amperka/abot/cad/MOTORS/12.SLDPRT

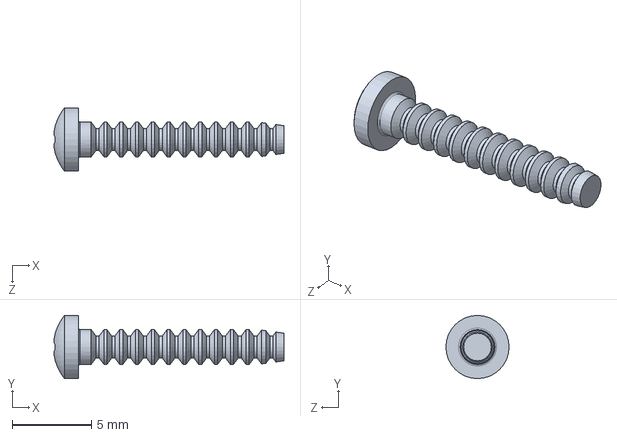
[picture p10: CAD file, 2021-09-09]
cad/MOTORS/12.SLDPRT
14.6 x 4.00 x 4.00 mm
