amperka/abot/cad/PARTS_PRINT/COMMON_PARTS/PRINT_PLATE_0.SLDPRT

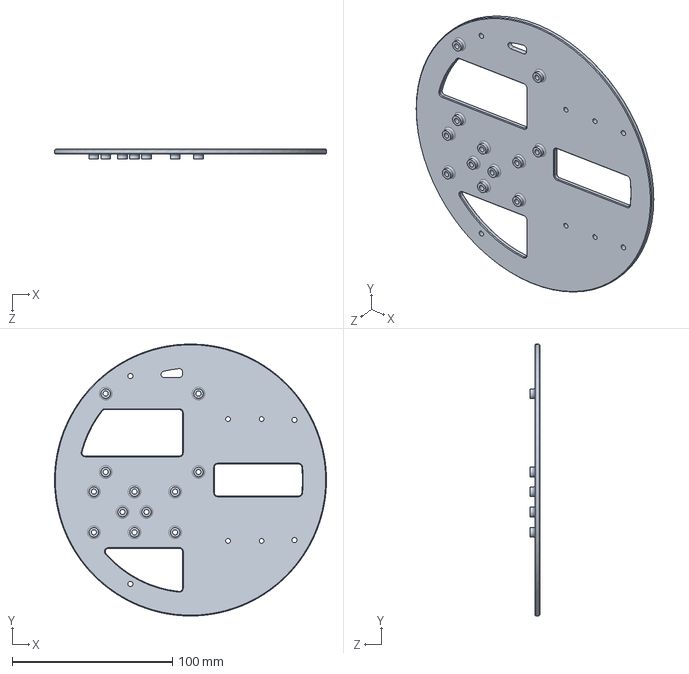
[picture p11: CAD file, 2021-09-09]
cad/PARTS_PRINT/COMMON_PARTS/PRINT_PLATE_0.SLDPRT
170.0 x 170.0 x 6.00 mm
