amperka/abot/cad/PARTS_PRINT/SHARP_IR_HOLDER.SLDPRT

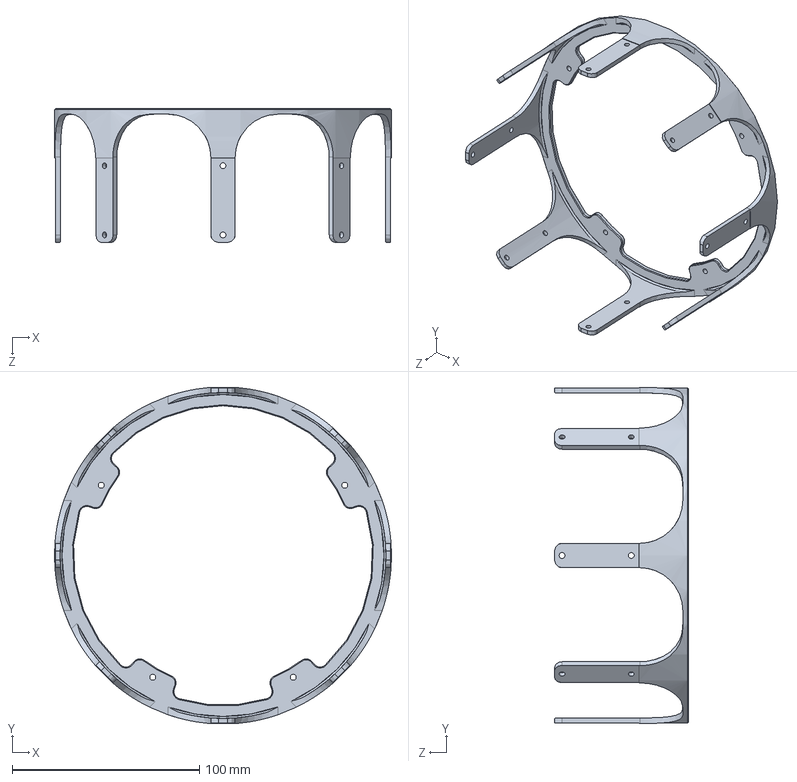
[picture p12: CAD file, 2021-09-09]
cad/PARTS_PRINT/SHARP_IR_HOLDER.SLDPRT
180.0 x 179.5 x 71.5 mm
