amperka/abot/cad/PARTS_PRINT/SOUND_PARTS/PRINT_MIC_CAP.SLDPRT

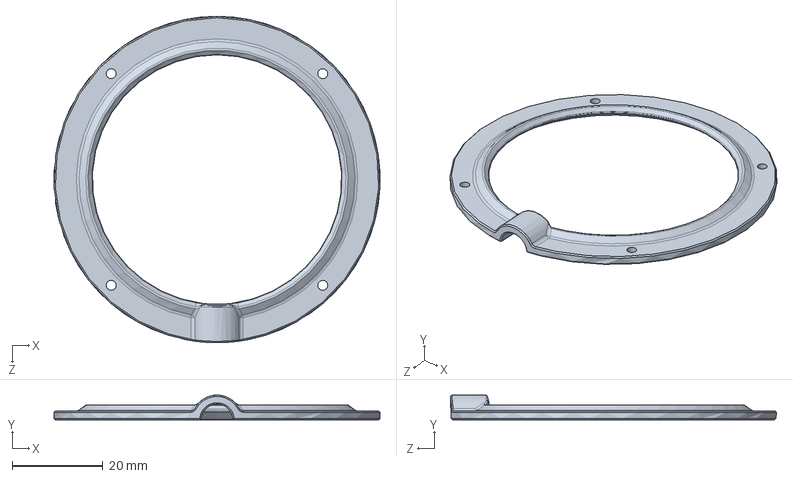
[picture p13: CAD file, 2021-09-09]
cad/PARTS_PRINT/SOUND_PARTS/PRINT_MIC_CAP.SLDPRT
71.9 x 5.50 x 72.0 mm
