amperka/abot/cad/SENSORS/LIDAR/18.SLDPRT

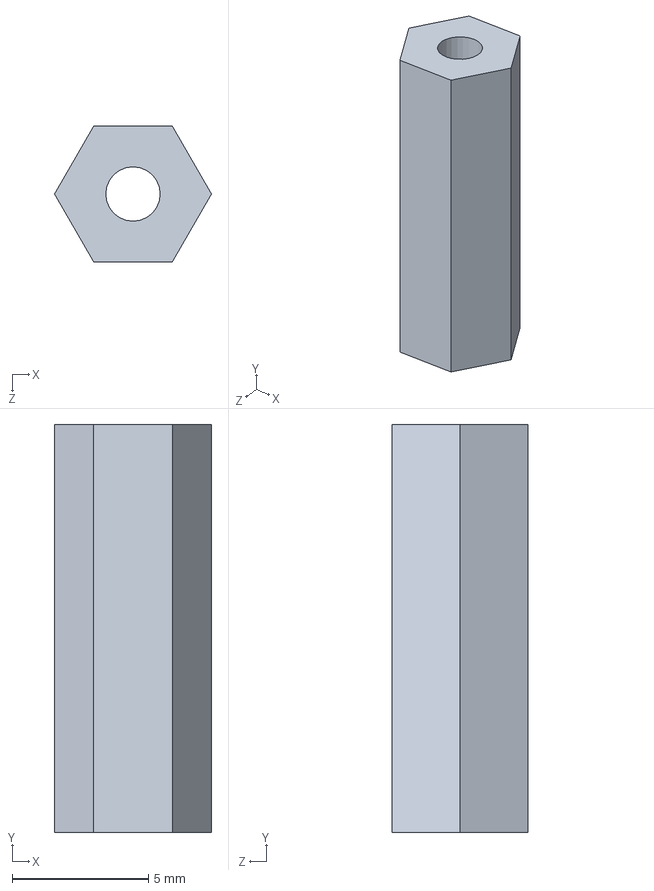
[picture p14: CAD file, 2021-09-09]
cad/SENSORS/LIDAR/18.SLDPRT
5.77 x 15.0 x 5.00 mm
