amperka/abot/cad/SOUND_DEVICES/CREATIVE_SOUND_BLASTER_PLAY_3.SLDPRT

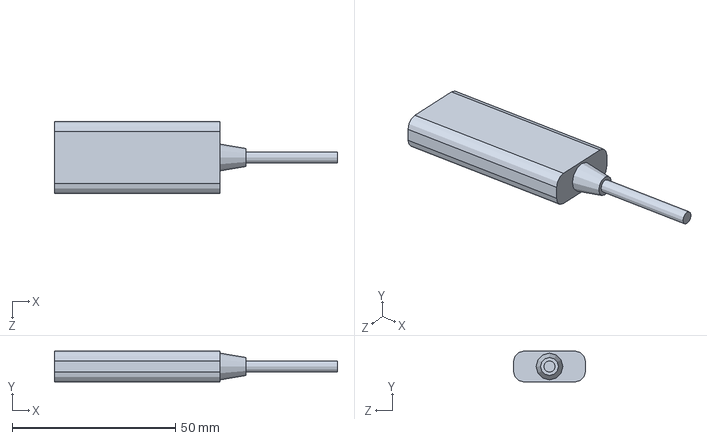
[picture p15: CAD file, 2021-09-09]
cad/SOUND_DEVICES/CREATIVE_SOUND_BLASTER_PLAY_3.SLDPRT
86.8 x 9.40 x 22.0 mm
