amperka/abot/ros/src/abot_description/meshes/abot_right_wheel.STL

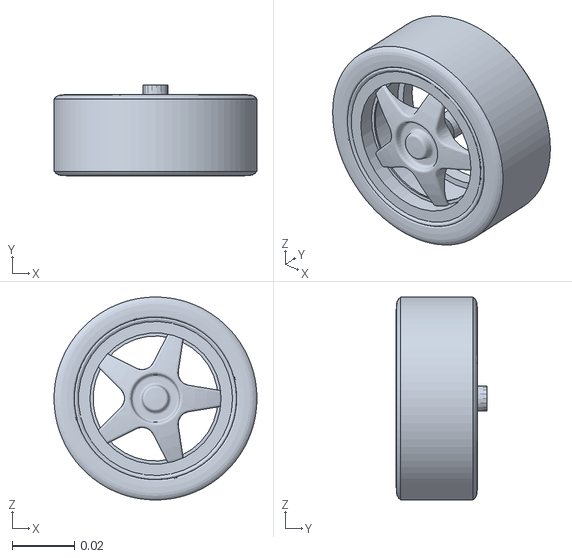
[picture p16: CAD file, 2021-09-09]
ros/src/abot_description/meshes/abot_right_wheel.STL
0.065 x 0.029 x 0.065
