amperka/abot/cad/CHASSIS/UPPER_PLATE.SLDPRT

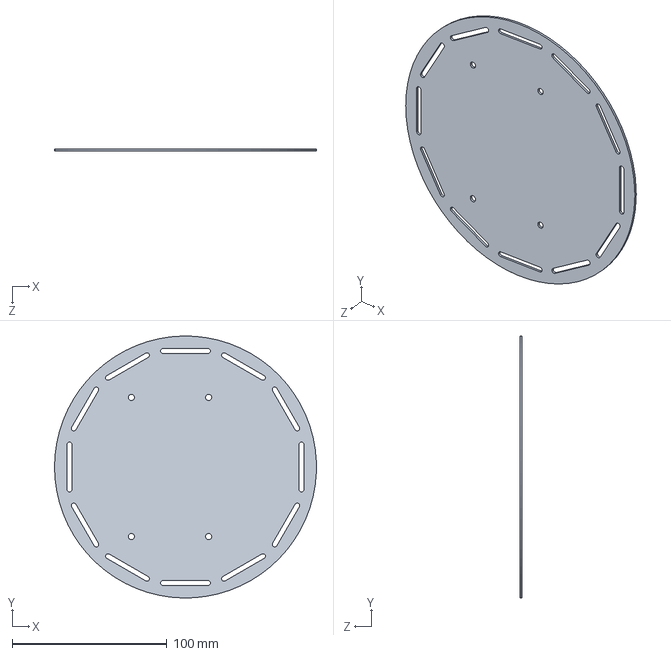
[picture p17: CAD file, 2021-09-09]
cad/CHASSIS/UPPER_PLATE.SLDPRT
169.5 x 169.5 x 1.40 mm
