amperka/abot/cad/METALWARE/STANDOFF_M3_50.SLDPRT

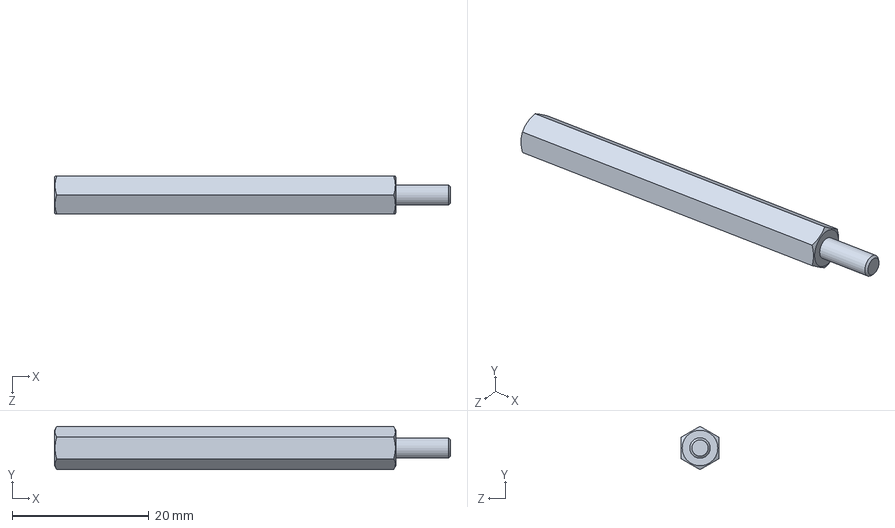
[picture p18: CAD file, 2021-09-09]
cad/METALWARE/STANDOFF_M3_50.SLDPRT
58.0 x 6.35 x 5.50 mm
