amperka/abot/cad/MOTORS/2.SLDPRT

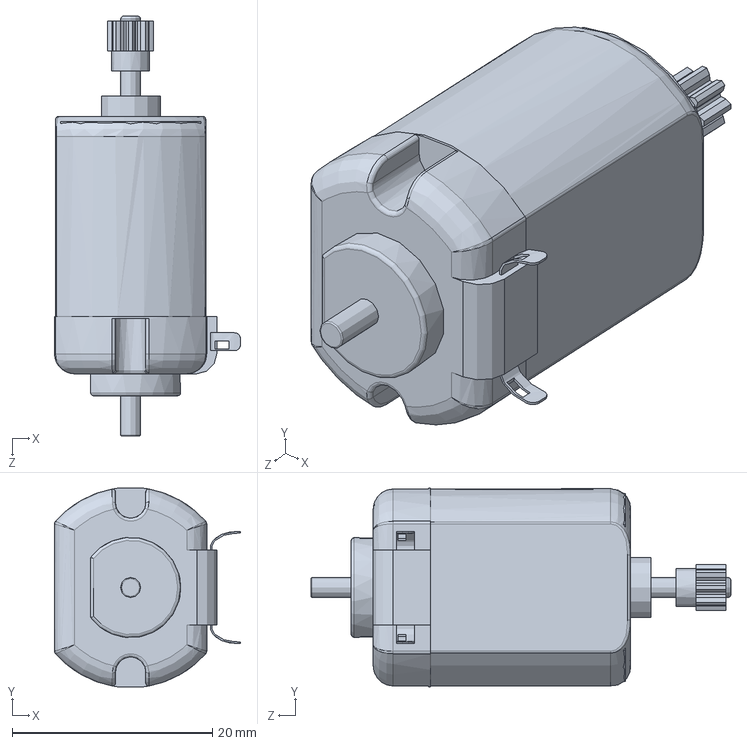
[picture p19: CAD file, 2021-09-09]
cad/MOTORS/2.SLDPRT
18.6 x 19.9 x 41.9 mm
