amperka/abot/cad/PARTS_PRINT/COMMON_PARTS/PRINT_PLATE_1.SLDPRT

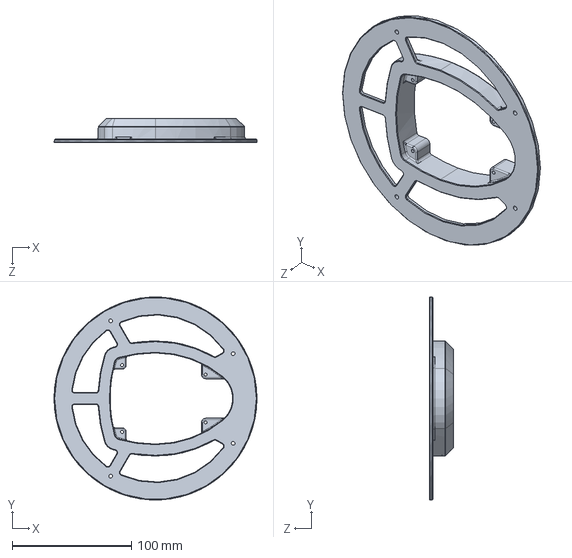
[picture p20: CAD file, 2021-09-09]
cad/PARTS_PRINT/COMMON_PARTS/PRINT_PLATE_1.SLDPRT
170.0 x 169.8 x 20.5 mm
