amperka/abot/cad/PARTS_PRINT/PRINT_PLATE_0.SLDPRT

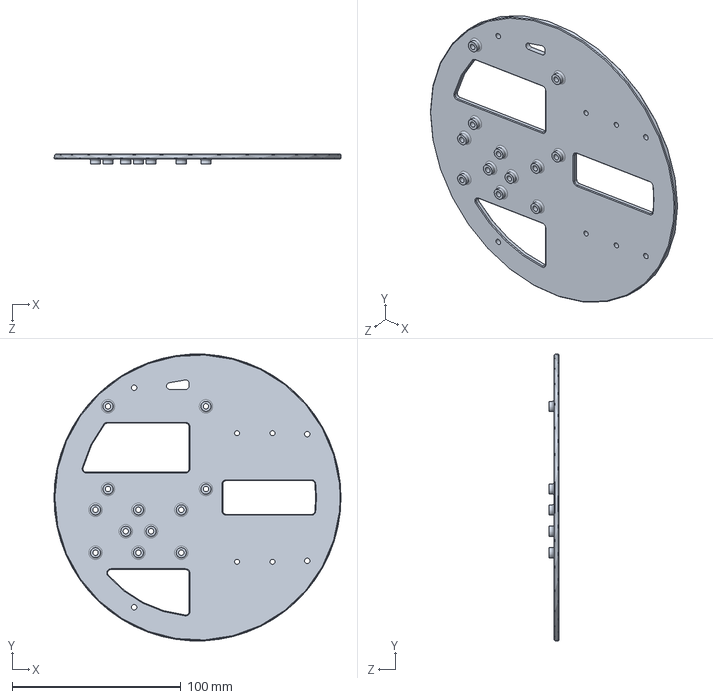
[picture p21: CAD file, 2021-09-09]
cad/PARTS_PRINT/PRINT_PLATE_0.SLDPRT
170.0 x 169.8 x 6.00 mm
