amperka/abot/cad/PARTS_PRINT/SOUND_PARTS/PRINT_PLATE_SOUND_0.SLDPRT

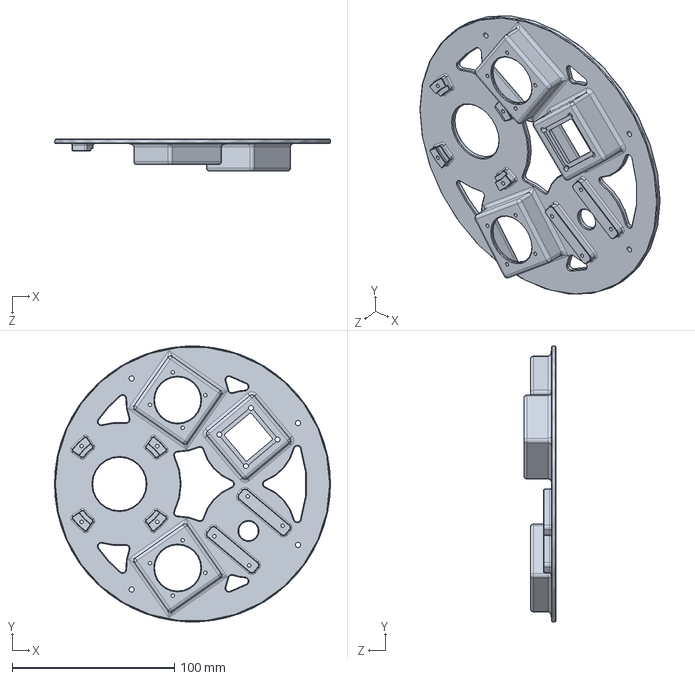
[picture p22: CAD file, 2021-09-09]
cad/PARTS_PRINT/SOUND_PARTS/PRINT_PLATE_SOUND_0.SLDPRT
170.0 x 169.8 x 20.0 mm
