amperka/abot/cad/SENSORS/LIDAR/21.SLDPRT

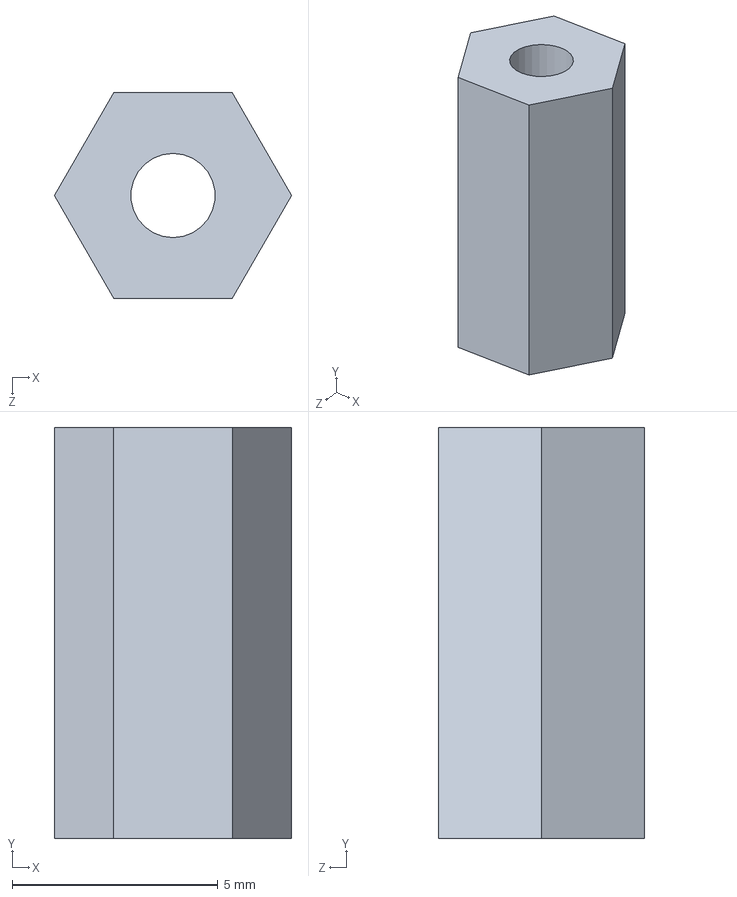
[picture p23: CAD file, 2021-09-09]
cad/SENSORS/LIDAR/21.SLDPRT
5.77 x 10.0 x 5.00 mm
