amperka/abot/cad/SOUND_DEVICES/TABLETOP_MICROPHONE_ATR4697.SLDPRT

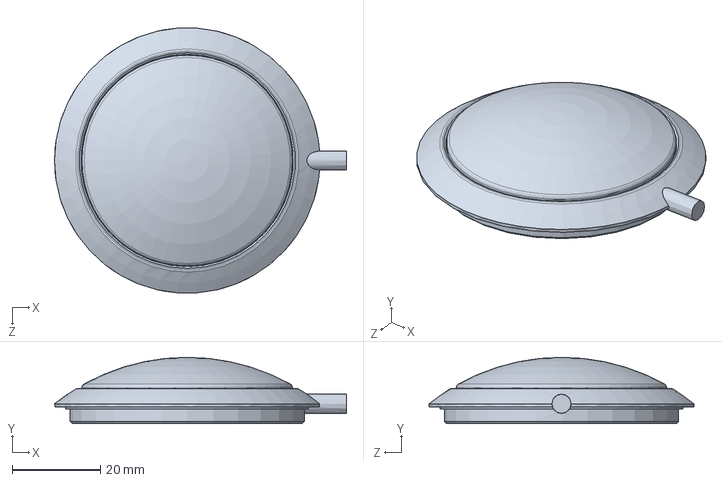
[picture p24: CAD file, 2021-09-09]
cad/SOUND_DEVICES/TABLETOP_MICROPHONE_ATR4697.SLDPRT
66.0 x 15.0 x 60.0 mm
