amperka/abot/cad/CHASSIS/WHEEL_D65_W26.SLDPRT

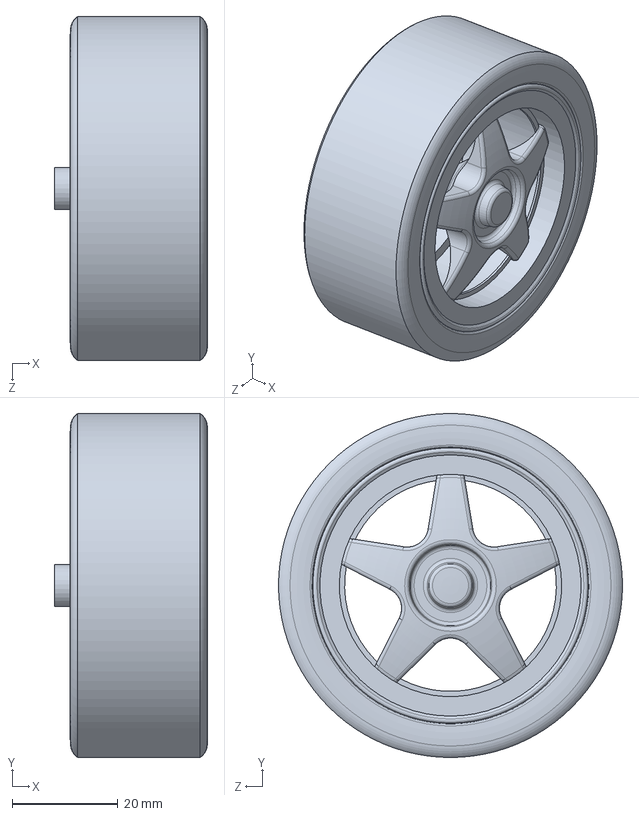
[picture p25: CAD file, 2021-09-09]
cad/CHASSIS/WHEEL_D65_W26.SLDPRT
29.0 x 65.0 x 65.0 mm
