amperka/abot/cad/METALWARE/STANDOFF_M3_60.SLDPRT

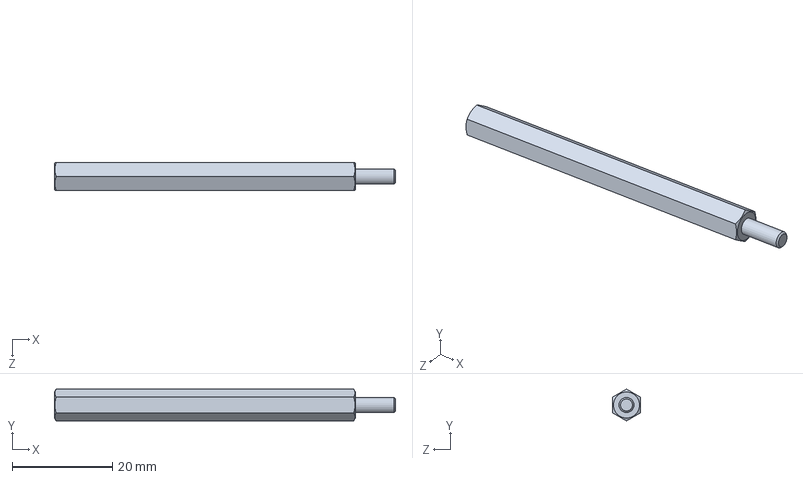
[picture p26: CAD file, 2021-09-09]
cad/METALWARE/STANDOFF_M3_60.SLDPRT
68.0 x 6.35 x 5.50 mm
