amperka/abot/cad/MOTORS/6.SLDPRT

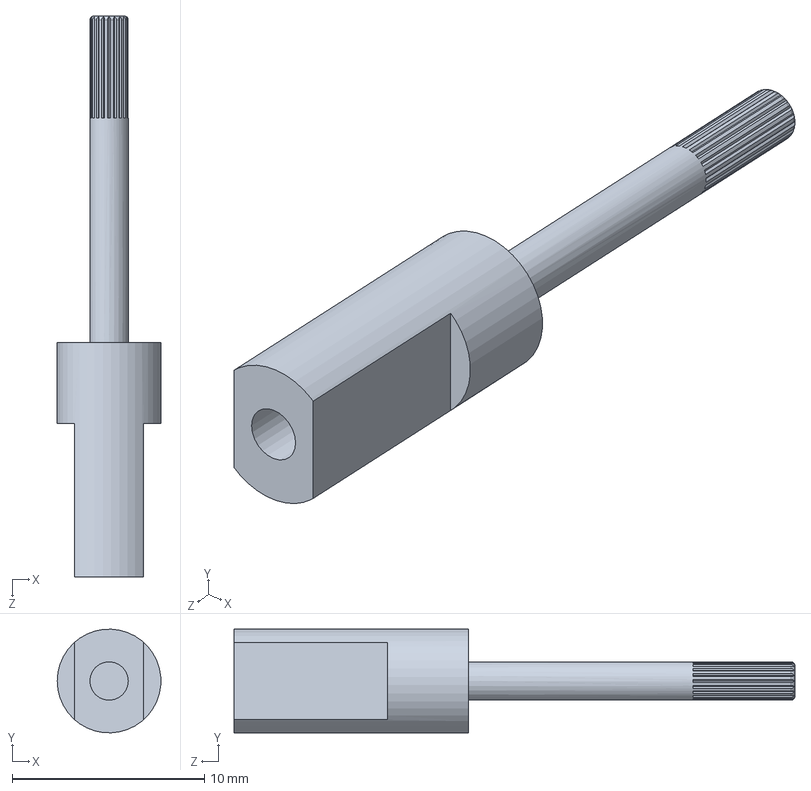
[picture p27: CAD file, 2021-09-09]
cad/MOTORS/6.SLDPRT
5.39 x 5.40 x 29.2 mm
