amperka/abot/cad/PARTS_PRINT/SOUND_PARTS/PRINT_SOUND_CARD_CAP.SLDPRT

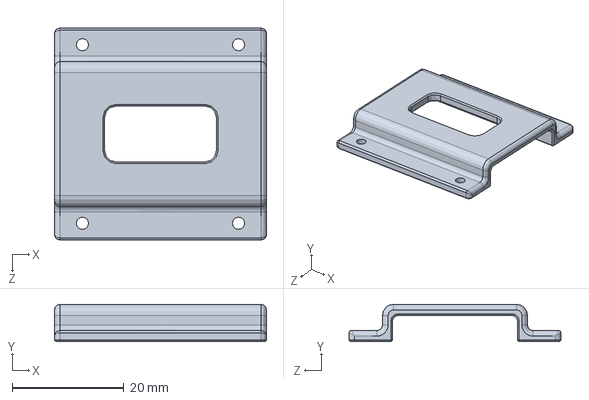
[picture p28: CAD file, 2021-09-09]
cad/PARTS_PRINT/SOUND_PARTS/PRINT_SOUND_CARD_CAP.SLDPRT
38.0 x 6.70 x 38.0 mm
