amperka/abot/cad/SENSORS/LIDAR/10.SLDPRT

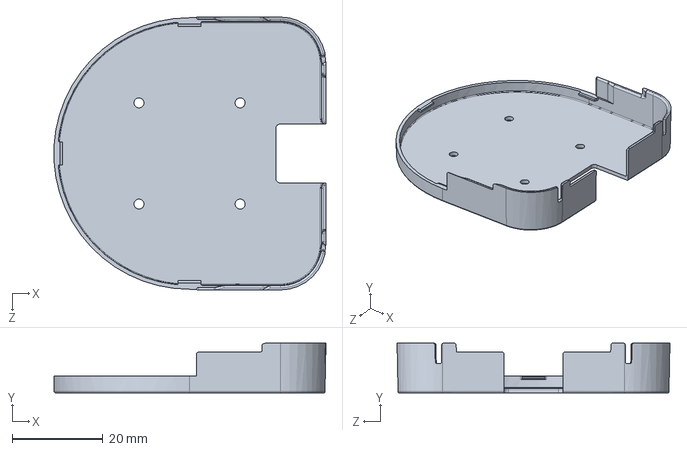
[picture p29: CAD file, 2021-09-09]
cad/SENSORS/LIDAR/10.SLDPRT
59.9 x 11.0 x 60.1 mm
