amperka/abot/cad/SOUND_DEVICES/VECO_32KC08_1.SLDPRT

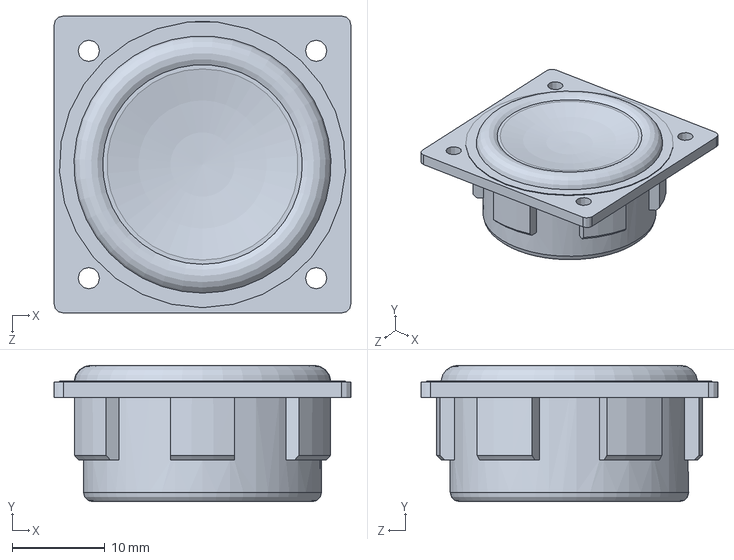
[picture p30: CAD file, 2021-09-09]
cad/SOUND_DEVICES/VECO_32KC08_1.SLDPRT
32.0 x 14.7 x 32.0 mm
