amperka/abot/ros/src/abot_description/meshes/v2/abot_caster_wheel.STL

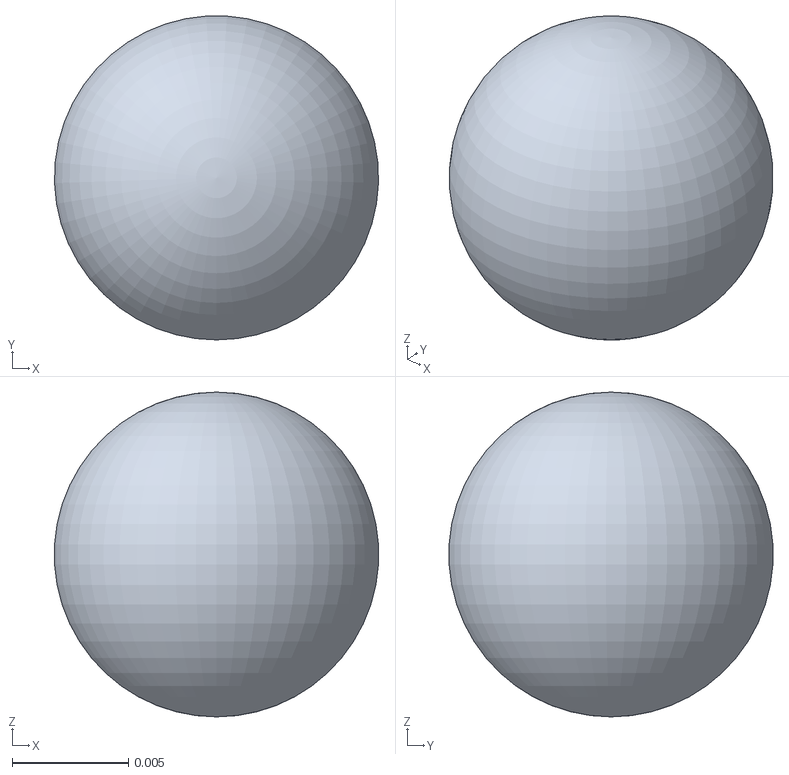
[picture p31: CAD file, 2021-09-09]
ros/src/abot_description/meshes/v2/abot_caster_wheel.STL
0.014 x 0.014 x 0.014
