amperka/abot/cad/CHASSIS/LOWER_PLATE.SLDPRT

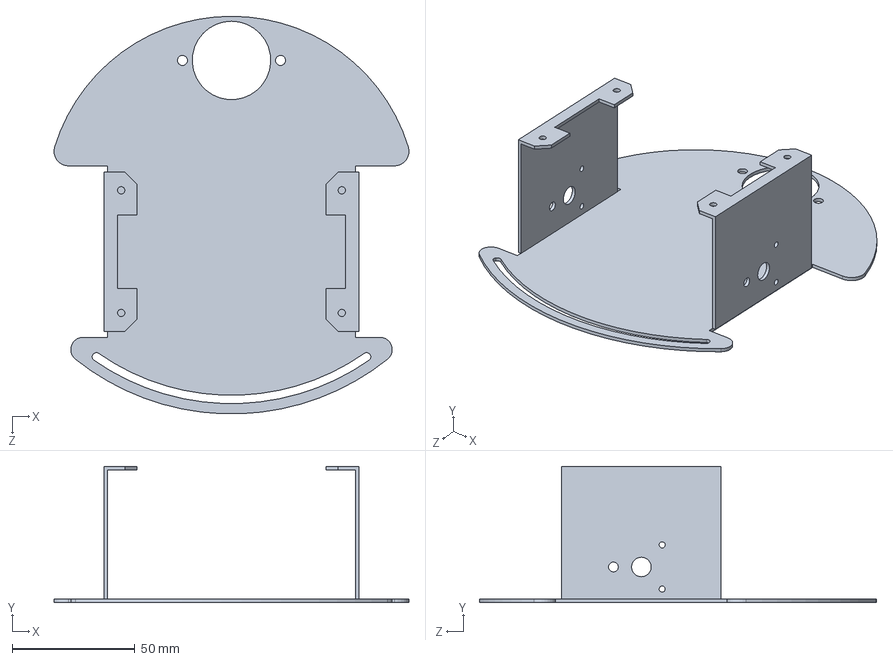
[picture p32: CAD file, 2021-09-09]
cad/CHASSIS/LOWER_PLATE.SLDPRT
144.8 x 55.5 x 162.1 mm
