amperka/abot/cad/MOTORS/15.SLDPRT

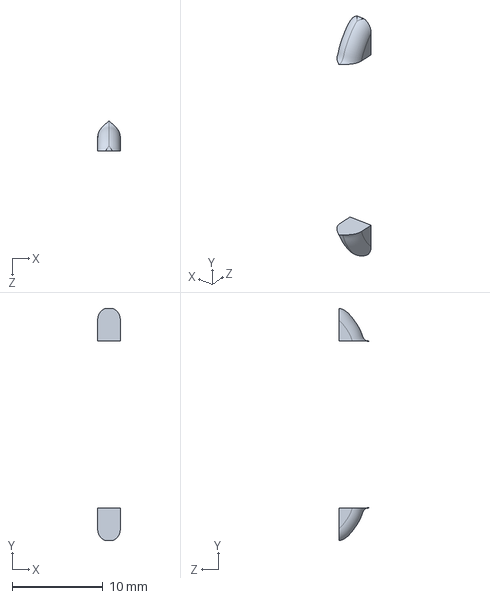
[picture p33: CAD file, 2021-09-09]
cad/MOTORS/15.SLDPRT
2.50 x 25.5 x 3.29 mm
