amperka/abot/cad/SENSORS/LIDAR/14.SLDPRT

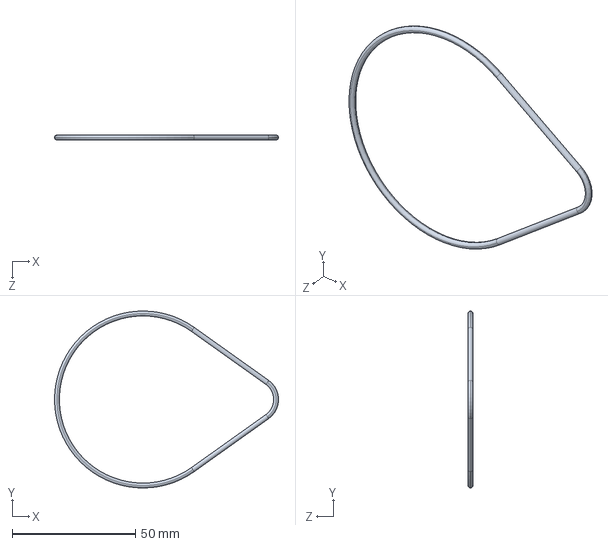
[picture p34: CAD file, 2021-09-09]
cad/SENSORS/LIDAR/14.SLDPRT
90.9 x 71.8 x 2.00 mm
