amperka/abot/cad/CHASSIS/CASTER_WHEEL_BALL.SLDPRT

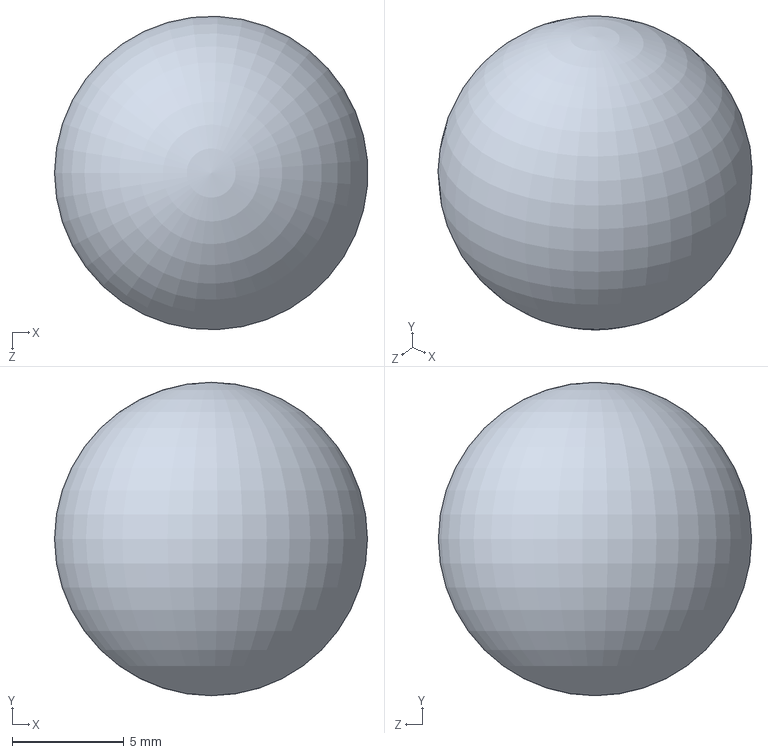
[picture p35: CAD file, 2021-09-09]
cad/CHASSIS/CASTER_WHEEL_BALL.SLDPRT
14.0 x 14.0 x 14.0 mm
