amperka/abot/cad/MOTORS/10.SLDPRT

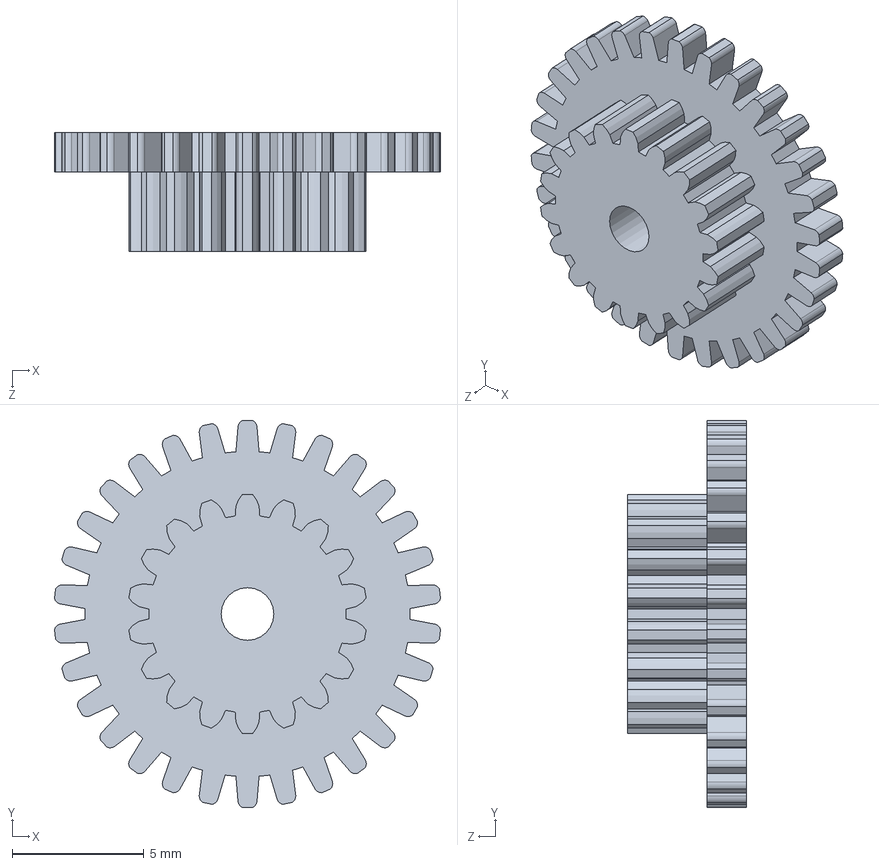
[picture p36: CAD file, 2021-09-09]
cad/MOTORS/10.SLDPRT
14.7 x 14.7 x 4.50 mm
