amperka/abot/cad/SENSORS/LIDAR/16.SLDPRT

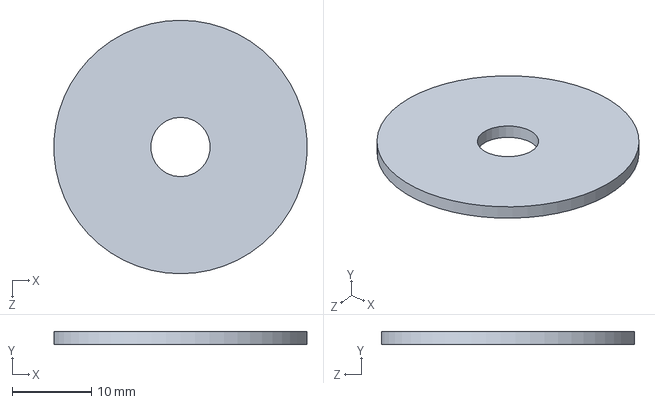
[picture p37: CAD file, 2021-09-09]
cad/SENSORS/LIDAR/16.SLDPRT
31.9 x 1.60 x 32.0 mm
