amperka/abot/cad/MOTORS/8.SLDPRT

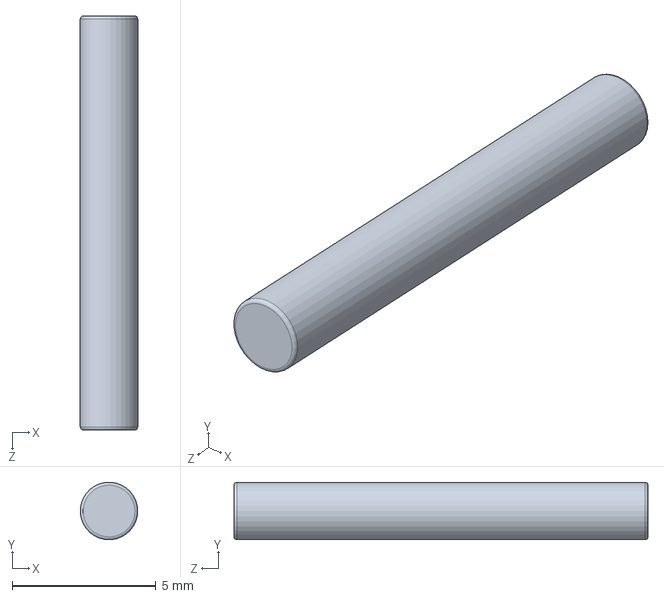
[picture p38: CAD file, 2021-09-09]
cad/MOTORS/8.SLDPRT
2.00 x 2.00 x 14.4 mm
