amperka/abot/cad/SENSORS/LIDAR/7.SLDPRT

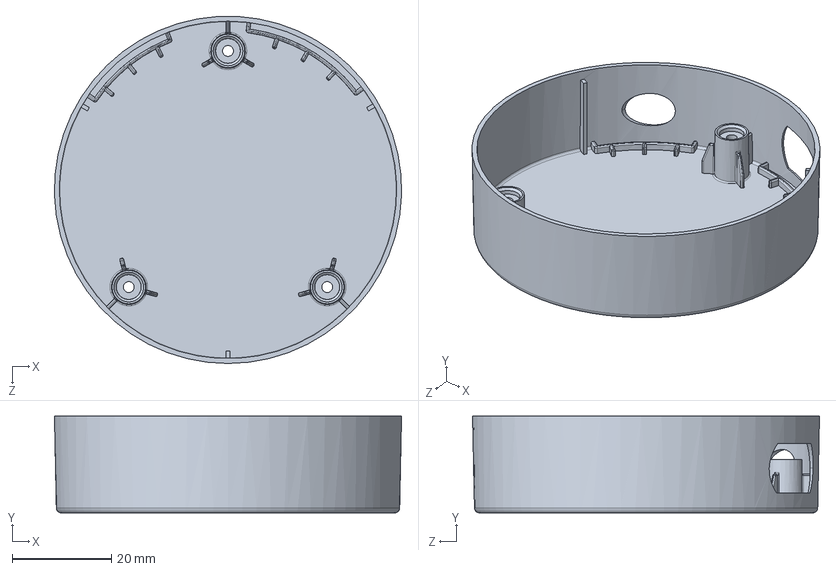
[picture p39: CAD file, 2021-09-09]
cad/SENSORS/LIDAR/7.SLDPRT
70.0 x 19.5 x 69.9 mm
