amperka/abot/cad/MOTORS/13.SLDPRT

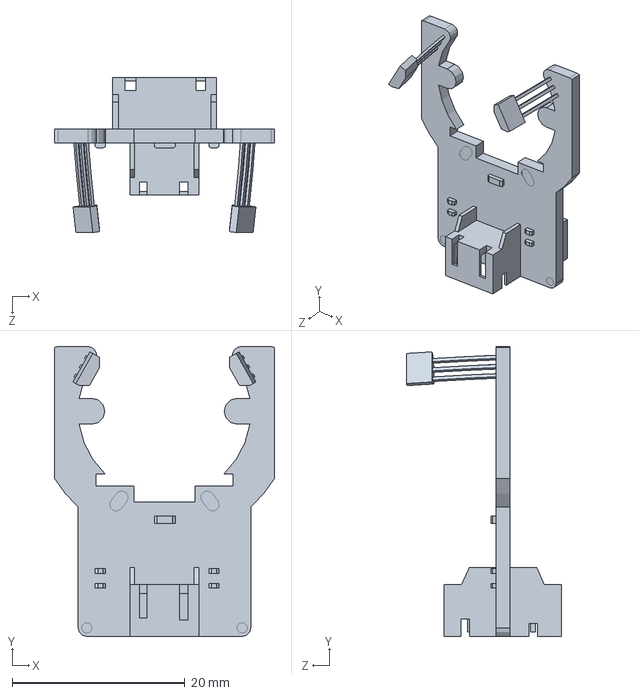
[picture p40: CAD file, 2021-09-09]
cad/MOTORS/13.SLDPRT
25.5 x 33.6 x 18.0 mm
