amperka/abot/cad/SENSORS/LIDAR/9.SLDPRT

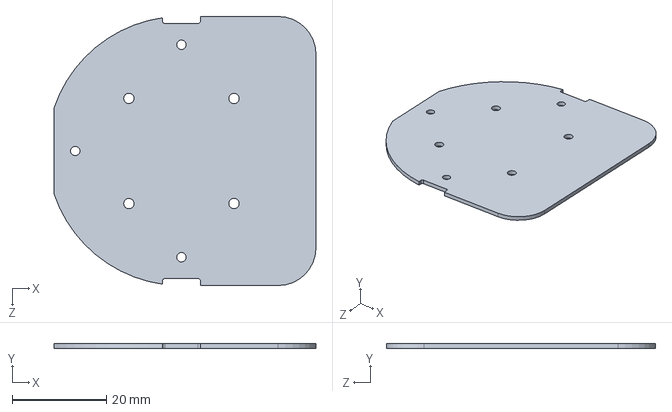
[picture p41: CAD file, 2021-09-09]
cad/SENSORS/LIDAR/9.SLDPRT
55.5 x 1.00 x 57.0 mm
