amperka/abot/cad/SENSORS/LIDAR/13.SLDPRT

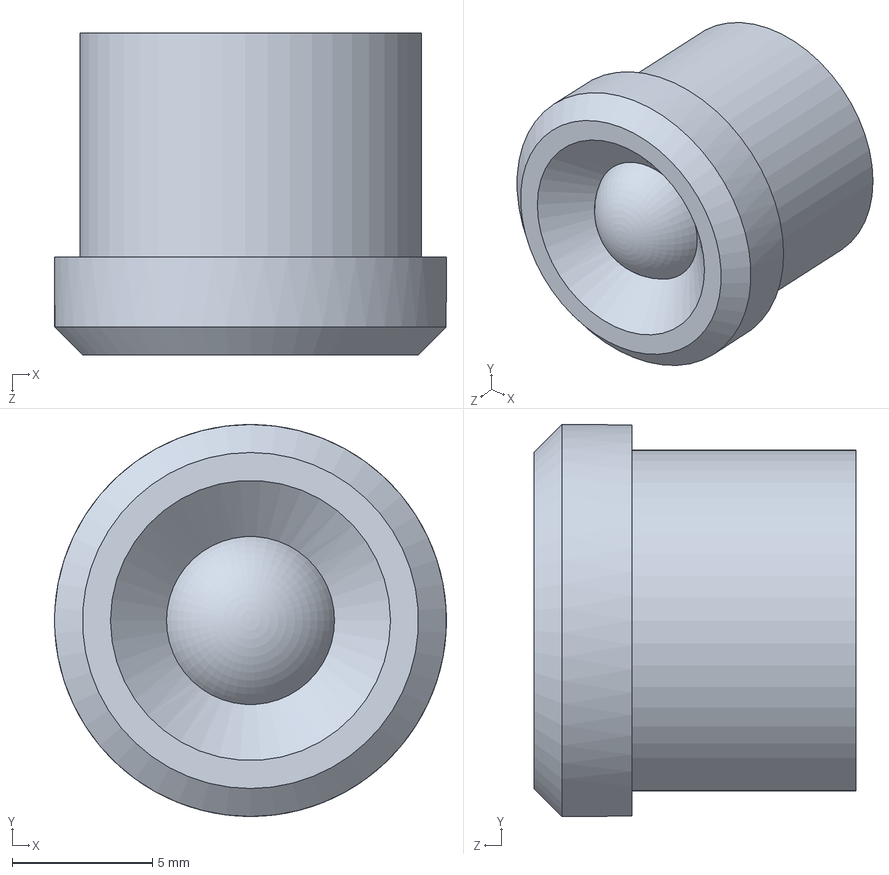
[picture p42: CAD file, 2021-09-09]
cad/SENSORS/LIDAR/13.SLDPRT
14.0 x 14.0 x 11.5 mm
