amperka/abot/cad/MOTORS/7.SLDPRT

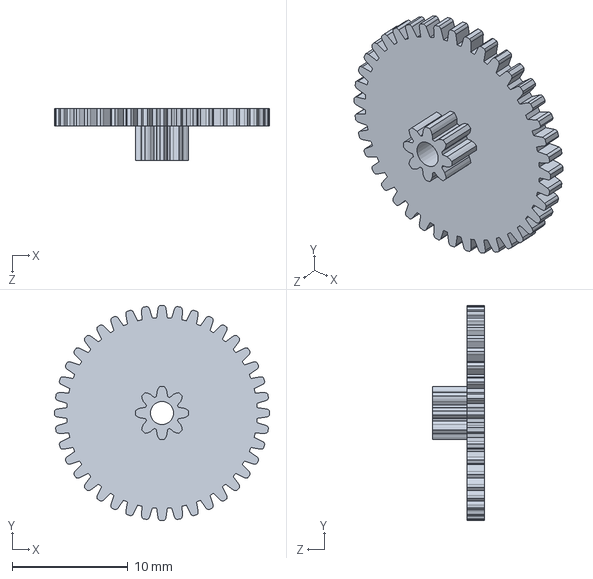
[picture p43: CAD file, 2021-09-09]
cad/MOTORS/7.SLDPRT
18.6 x 18.6 x 4.50 mm
