amperka/abot/cad/SENSORS/LIDAR/6.SLDPRT

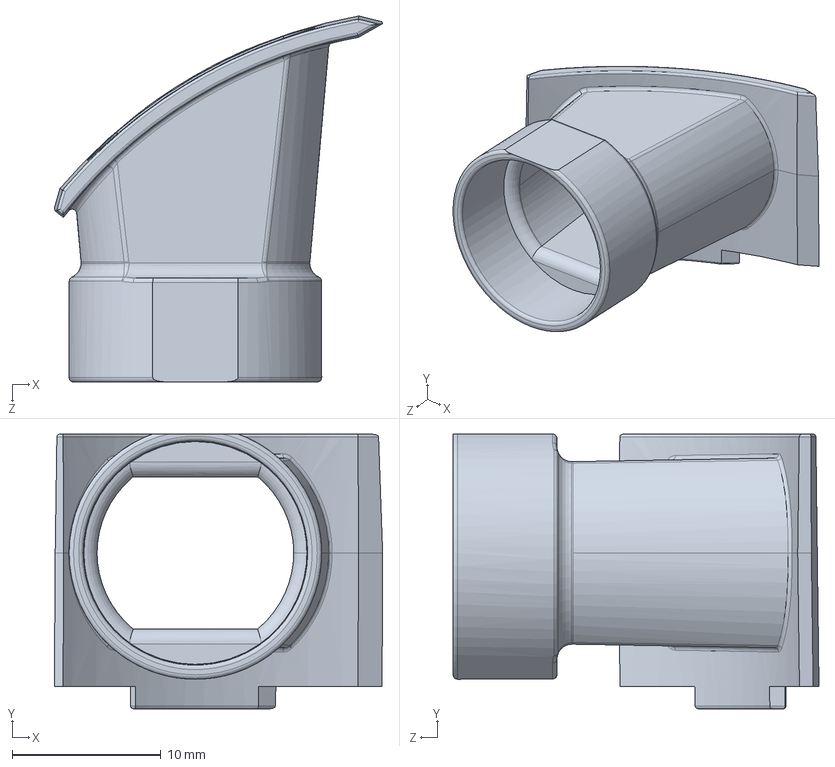
[picture p44: CAD file, 2021-09-09]
cad/SENSORS/LIDAR/6.SLDPRT
22.1 x 18.5 x 24.6 mm
