amperka/abot/cad/MOTORS/14.SLDPRT

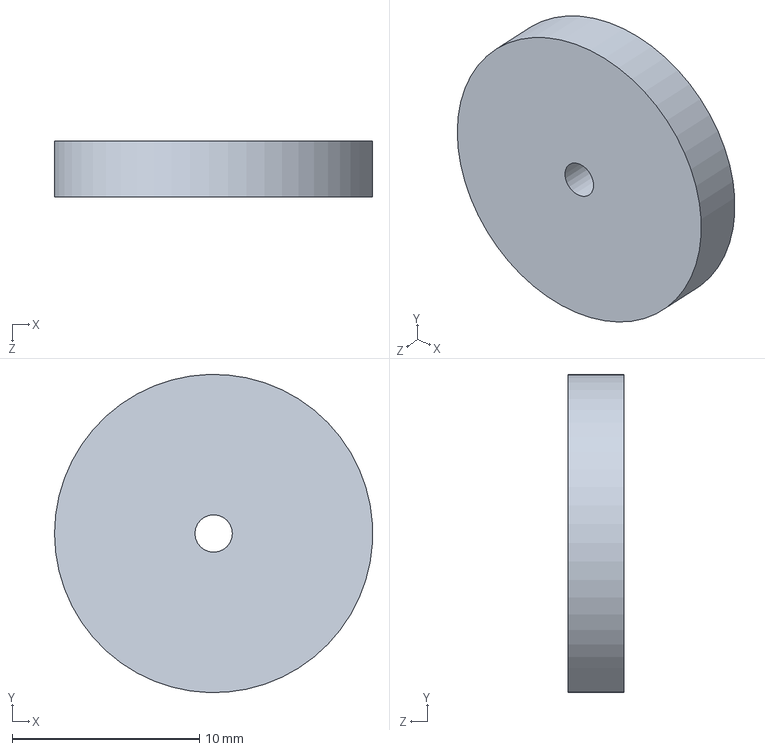
[picture p45: CAD file, 2021-09-09]
cad/MOTORS/14.SLDPRT
17.0 x 17.0 x 3.00 mm
