amperka/abot/cad/SENSORS/LIDAR/1.SLDPRT

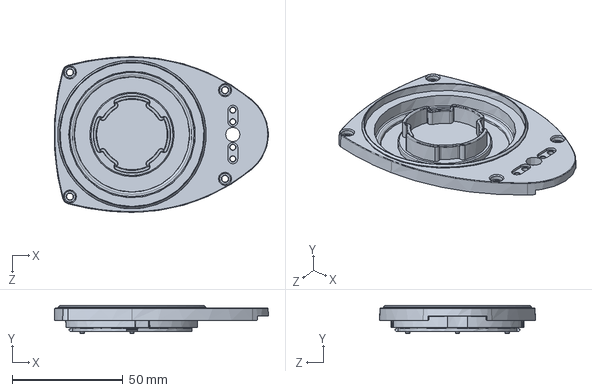
[picture p46: CAD file, 2021-09-09]
cad/SENSORS/LIDAR/1.SLDPRT
96.6 x 12.7 x 70.3 mm
