amperka/abot/cad/MOTORS/4.SLDPRT

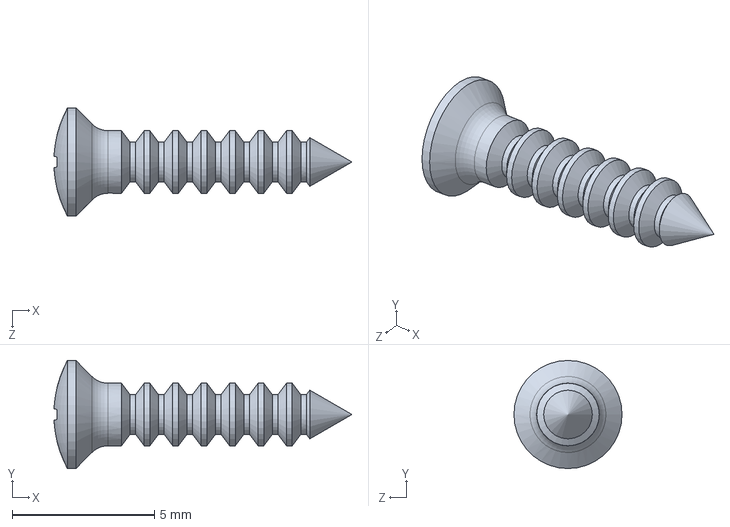
[picture p47: CAD file, 2021-09-09]
cad/MOTORS/4.SLDPRT
10.5 x 3.80 x 3.80 mm
