amperka/abot/cad/SENSORS/LIDAR/12.SLDPRT

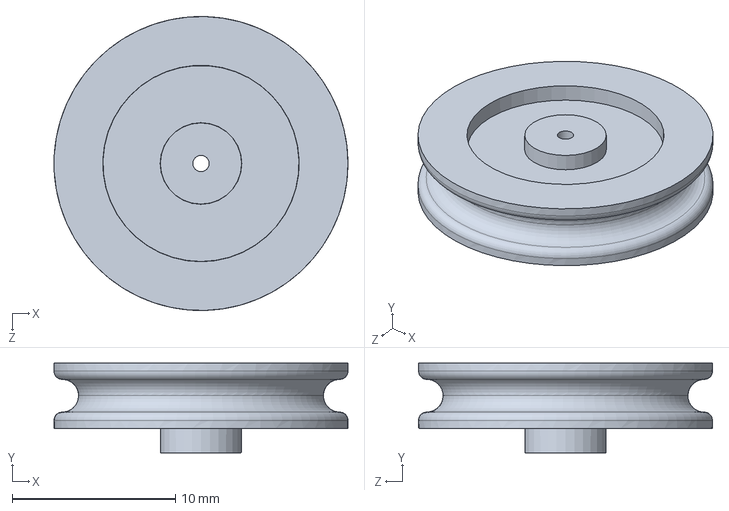
[picture p48: CAD file, 2021-09-09]
cad/SENSORS/LIDAR/12.SLDPRT
18.0 x 5.50 x 18.0 mm
