amperka/abot/cad/SENSORS/LIDAR/4.SLDPRT

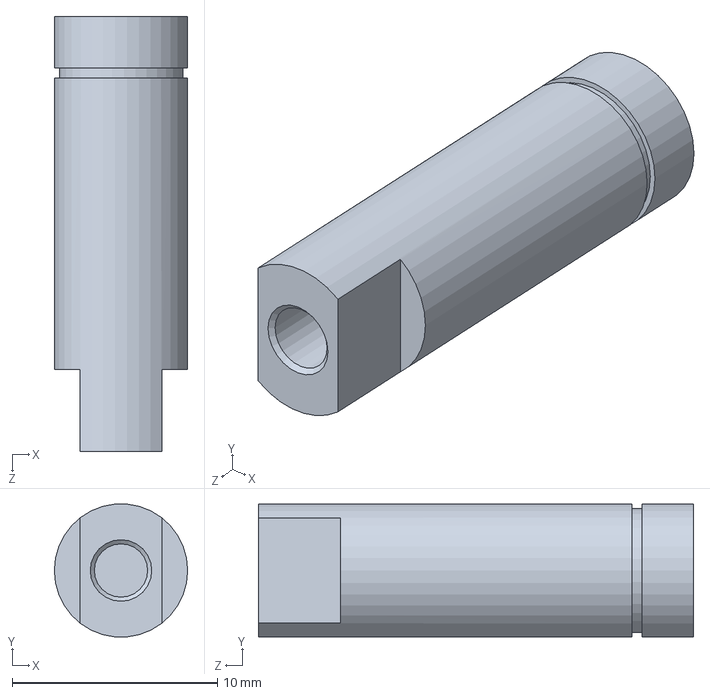
[picture p49: CAD file, 2021-09-09]
cad/SENSORS/LIDAR/4.SLDPRT
6.50 x 6.47 x 21.2 mm
