amperka/abot/cad/MOTORS/11.SLDPRT

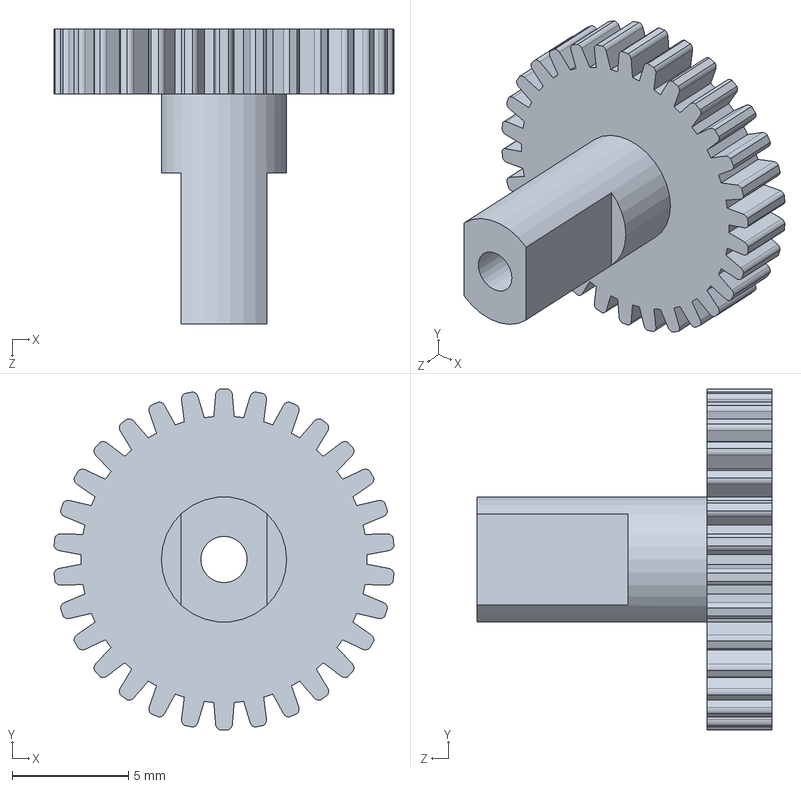
[picture p50: CAD file, 2021-09-09]
cad/MOTORS/11.SLDPRT
14.7 x 14.7 x 12.7 mm
