amperka/abot/cad/SENSORS/LIDAR/17.SLDPRT

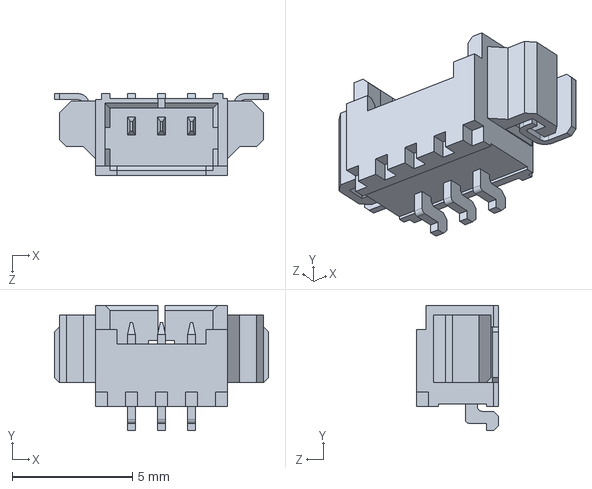
[picture p51: CAD file, 2021-09-09]
cad/SENSORS/LIDAR/17.SLDPRT
8.90 x 5.20 x 3.40 mm
