amperka/abot/cad/MOTORS/5.SLDPRT

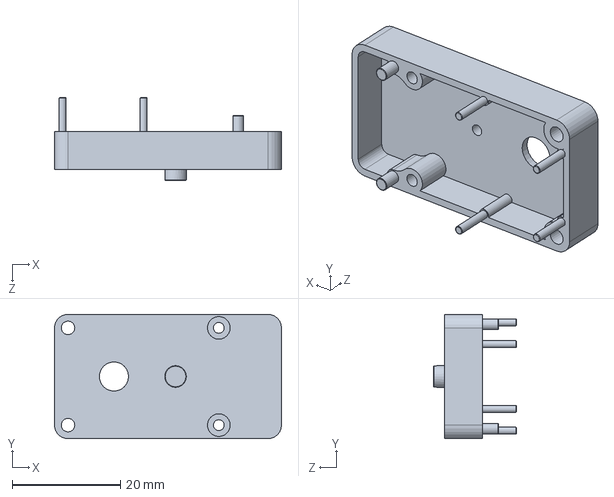
[picture p52: CAD file, 2021-09-09]
cad/MOTORS/5.SLDPRT
42.0 x 23.0 x 15.3 mm
