amperka/abot/cad/SENSORS/LIDAR/19.SLDPRT

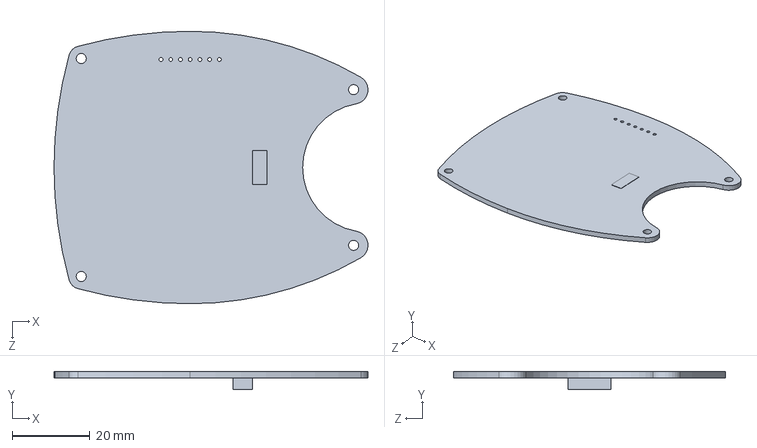
[picture p53: CAD file, 2021-09-09]
cad/SENSORS/LIDAR/19.SLDPRT
80.7 x 4.70 x 70.0 mm
