amperka/abot/cad/MOTORS/3.SLDPRT

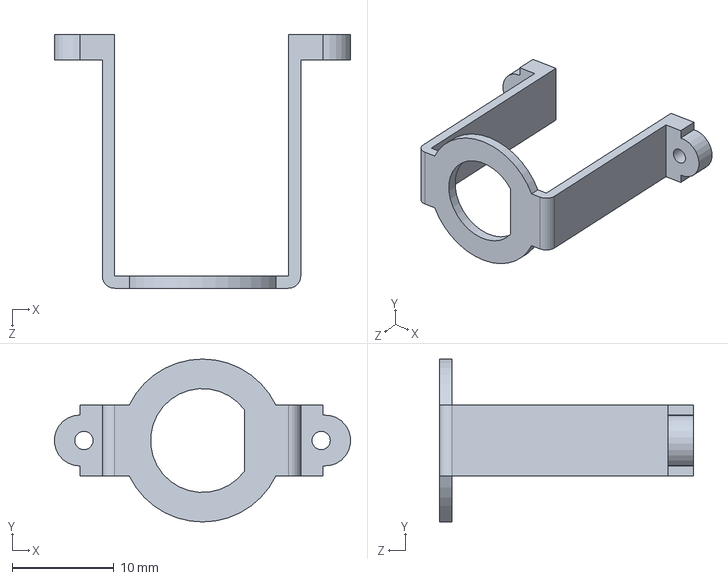
[picture p54: CAD file, 2021-09-09]
cad/MOTORS/3.SLDPRT
29.1 x 16.0 x 24.9 mm
