amperka/abot/cad/SENSORS/LIDAR/22.SLDPRT

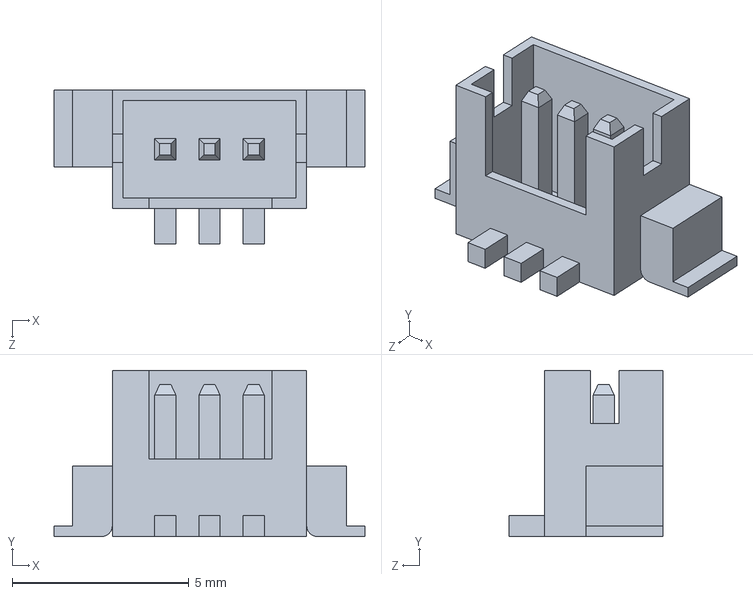
[picture p55: CAD file, 2021-09-09]
cad/SENSORS/LIDAR/22.SLDPRT
8.80 x 4.70 x 4.36 mm
