amperka/abot/cad/MOTORS/1.SLDPRT

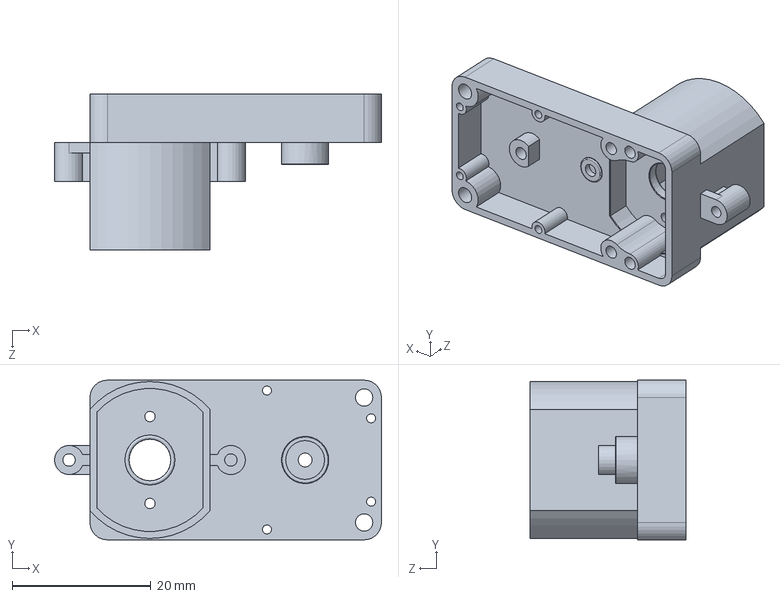
[picture p56: CAD file, 2021-09-09]
cad/MOTORS/1.SLDPRT
47.1 x 23.0 x 22.5 mm
