amperka/abot/cad/SENSORS/LIDAR/5.SLDPRT

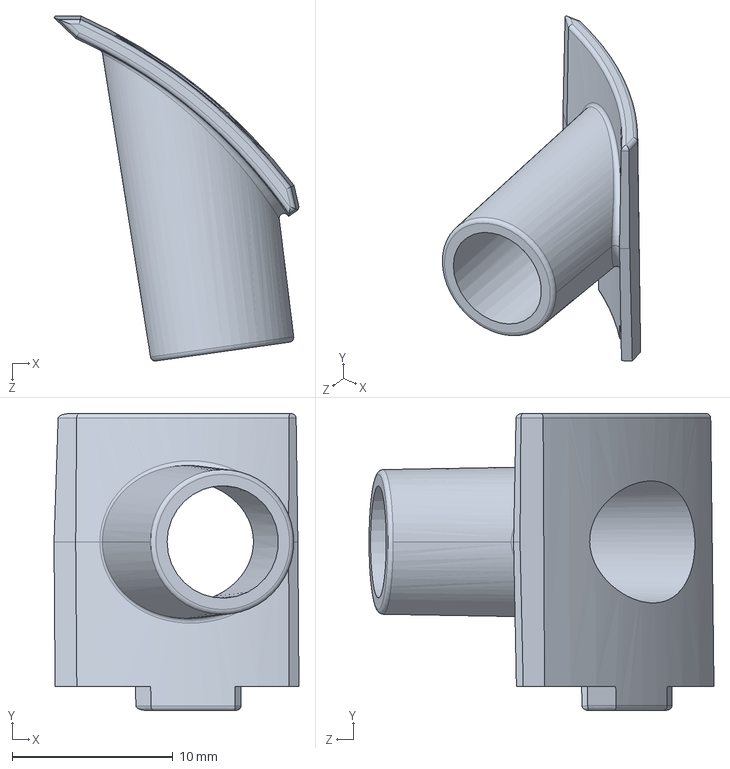
[picture p57: CAD file, 2021-09-09]
cad/SENSORS/LIDAR/5.SLDPRT
15.3 x 18.5 x 21.5 mm
