amperka/abot/cad/MOTORS/9.SLDPRT

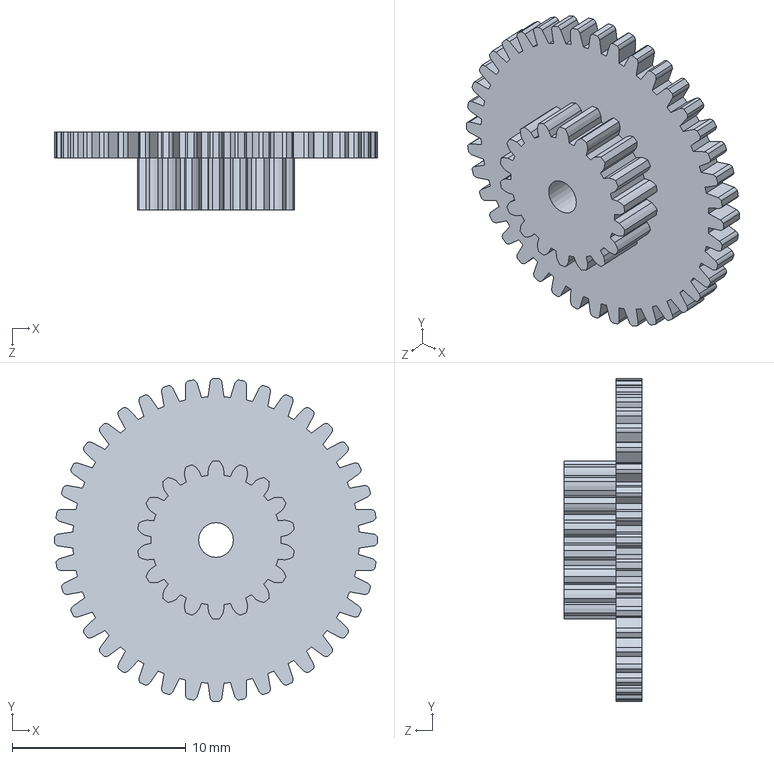
[picture p58: CAD file, 2021-09-09]
cad/MOTORS/9.SLDPRT
18.6 x 18.6 x 4.50 mm
