amperka/abot/cad/SENSORS/LIDAR/3.SLDPRT

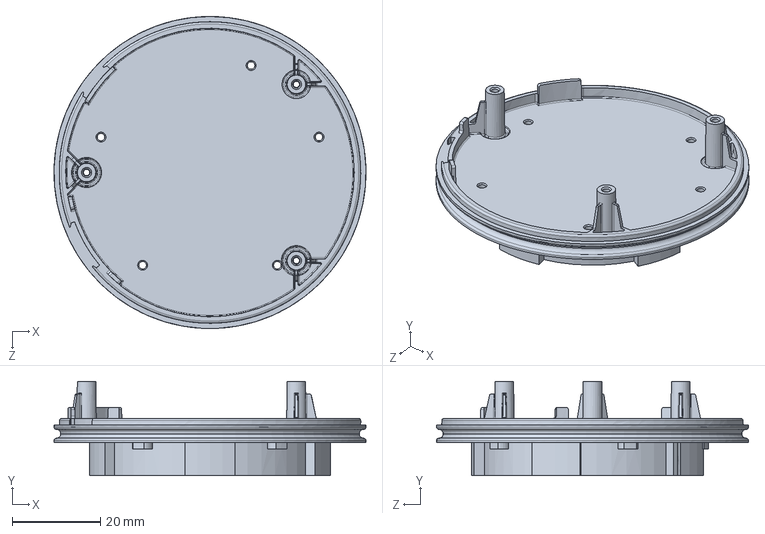
[picture p59: CAD file, 2021-09-09]
cad/SENSORS/LIDAR/3.SLDPRT
70.8 x 21.4 x 70.8 mm
