amperka/abot/cad/SENSORS/LIDAR/11.SLDPRT

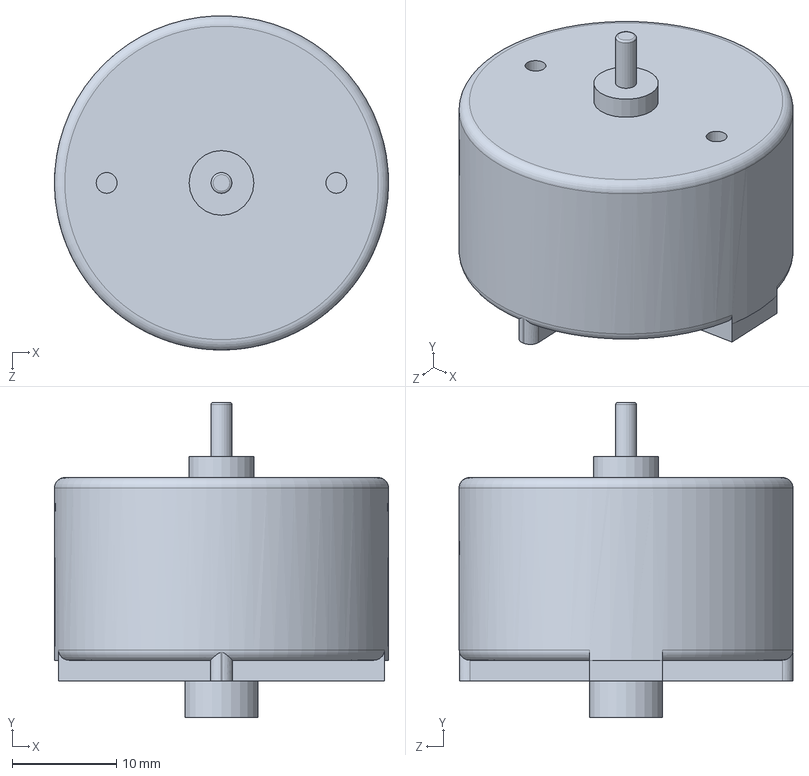
[picture p60: CAD file, 2021-09-09]
cad/SENSORS/LIDAR/11.SLDPRT
32.0 x 30.2 x 32.0 mm
