amperka/abot/cad/SENSORS/LIDAR/2.SLDPRT

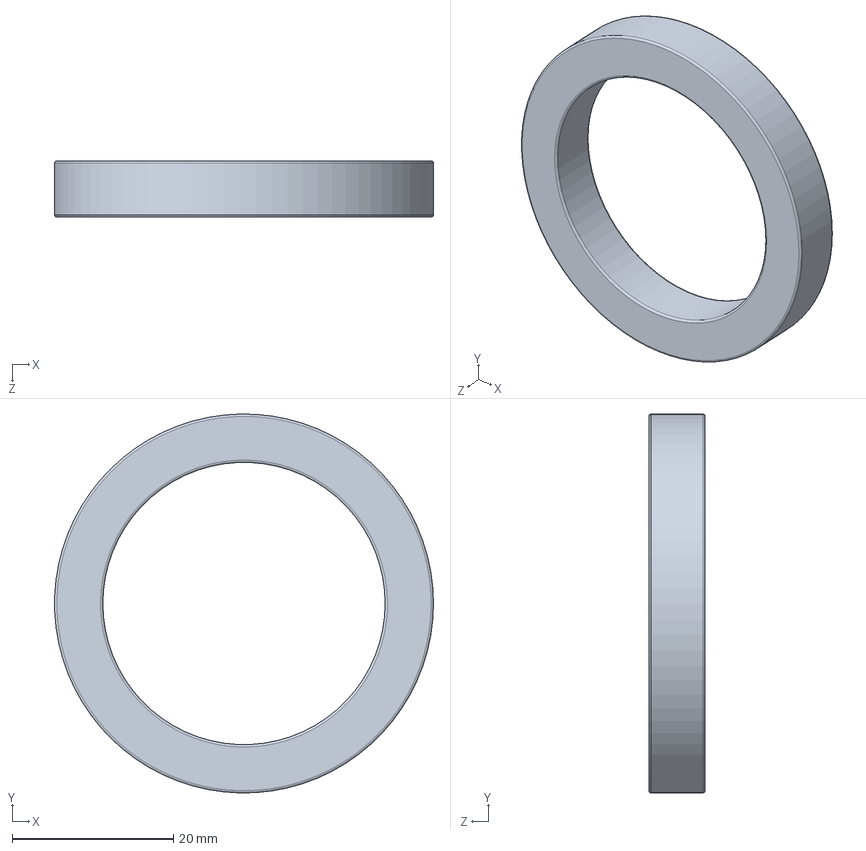
[picture p61: CAD file, 2021-09-09]
cad/SENSORS/LIDAR/2.SLDPRT
47.0 x 47.0 x 7.00 mm
