amperka/abot/cad/SENSORS/LIDAR/20.SLDPRT

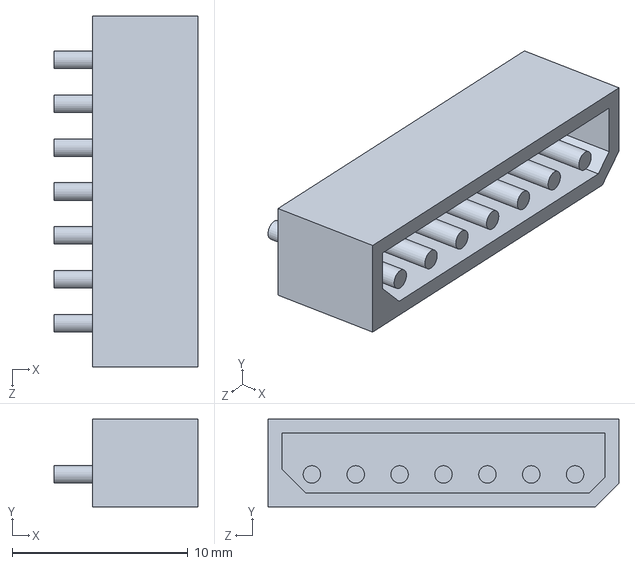
[picture p62: CAD file, 2021-09-09]
cad/SENSORS/LIDAR/20.SLDPRT
8.20 x 5.00 x 20.0 mm
