amperka/abot/cad/SENSORS/LIDAR/8.SLDPRT

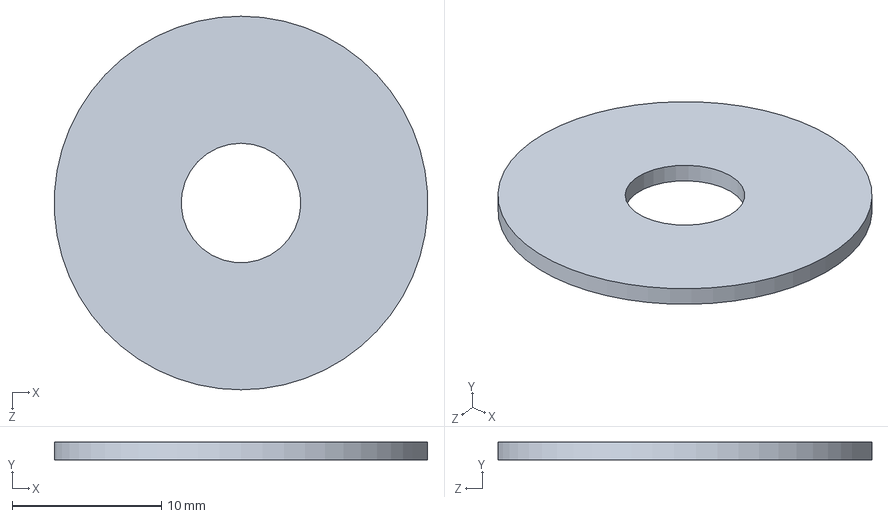
[picture p63: CAD file, 2021-09-09]
cad/SENSORS/LIDAR/8.SLDPRT
25.0 x 1.20 x 25.0 mm
