amperka/abot/cad/SENSORS/LIDAR/15.SLDPRT

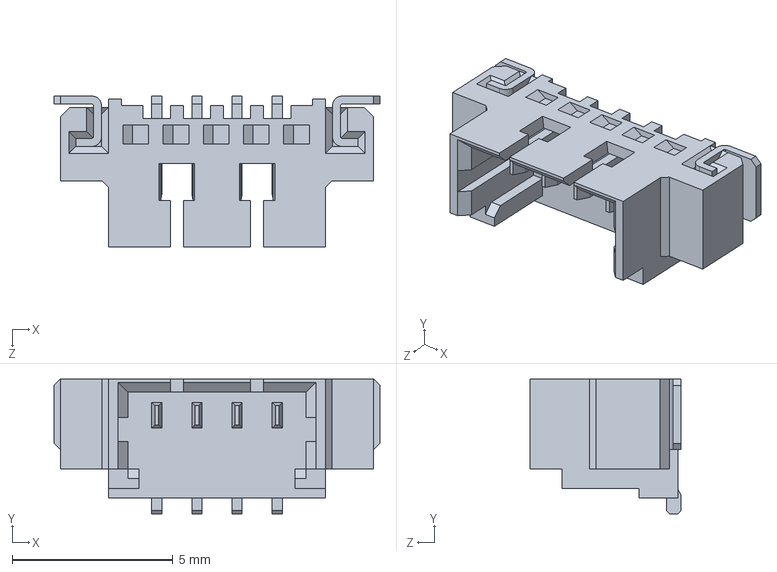
[picture p64: CAD file, 2021-09-09]
cad/SENSORS/LIDAR/15.SLDPRT
10.2 x 4.20 x 4.70 mm
