amperka/abot/ros/src/abot_slam/config/gmapping_params.yaml

base_frame: base_footprint
odom_frame: odom
map_frame: map

map_update_interval: 1.0
maxUrange: 7.0

linearUpdate: 0.2
angularUpdate: 0.5
temporalUpdate: 0.2
resampleThreshold: 0.5

particles: 30

xmax: 20.0
xmin: -20.0
ymax: 20.0
ymin: -20.0

delta: 0.025

# Keep default
sigma: 0.05
kernelSize: 1
lstep: 0.05
astep: 0.05
iterations: 5
lsigma: 0.075
ogain: 3.0
lskip: 0

srr: 0.1
srt: 0.2
str: 0.1
stt: 0.2

llsamplerange: 0.01
llsamplestep: 0.01
lasamplerange: 0.005
lasamplestep: 0.005
