amperka/abot/ros/src/abot_sound/abot_speech_command/src/vc_get_system_time.cpp

#include "vc_get_system_time.h"
#include <ros/ros.h>

int main(int argc, char** argv) {
	ros::init(argc, argv, "vc_get_system_time");
	VCGetSystemTime get_system_time;
	ROS_INFO("Voice command node 'Get System Time': Start.");
	ros::spin();
	return 0;
}
