amperka/abot/ros/src/abot_sound/abot_speech_command/src/vc_set_navigation_goal.cpp

#include "vc_set_navigation_goal.h"
#include <ros/ros.h>

int main(int argc, char** argv) {
	ros::init(argc, argv, "vc_set_navigation_goal");
	VCSetNavigationGoal set_navigation_goal;
	ROS_INFO("Voice command node 'Set Navigation Goal': Start.");
	ros::spin();
	return 0;
}
